jmkao/rfglow/arduino/rfglow_esp32/src/leds.cpp

#include "leds.h"

// TLC59116 Setup
TLC59116Manager tlcmanager(Wire, 30000L);
TLC59116* driver = NULL;

// LED state
int mH = 0;
int mS = 255;
int mB = 0;

unsigned int ma = 61;

// Targets for fading
target_color target = {mH, mS, mB, 0};

int target_maLevel = 1;
long fade_dH = 0, fade_dS = 0, fade_dV = 0;
unsigned long fade_start_ms = 0;

boolean isAutoCycle = false;

unsigned long prevMs = 0;

void initLEDs() {
  // Init TLC59116
  tlcmanager.init();
  DEBUG_PRINTLN("tlcmanager init complete");
  
  driver = &(tlcmanager[0]);
  driver->enable_outputs(true);
  DEBUG_PRINTLN("tlcmanager enable_outputs");
  driver->set_milliamps(ma);
}

void ledTick() {
  unsigned long curMs = millis();

  if (curMs - prevMs < LED_TICK_INTERVAL) {
    return;
  }

  if (isAutoCycle) {
    if (curMs - prevMs > AUTO_INTERVAL) {
      target.h = (target.h + 60) % 360;
    }
  }

  if (fade_start_ms == 0 || target.ms == 0  // No fade in progress
      || curMs - fade_start_ms > 60000  //Fade timed out, more than 60s elapsed
      || curMs - fade_start_ms > target.ms  //Fade reached the end
      ) {
    mH = target.h;
    mS = target.s;
    mB = target.v;
    fade_start_ms = 0;
    target.ms = 0;
  } else if (target.ms == 65535) {
    // Code for UO decay
  } else {
    // In the middle of a linear fade
    long dT = curMs - fade_start_ms;
    long ratio = 10000 - (dT * 10000 / target.ms);
    //DEBUG_PRINTLN("Fade at "+ratio/100+"%");
    int dH = ratio * fade_dH / 10000;
    int dS = ratio * fade_dS / 10000;
    int dV = ratio * fade_dV / 10000;

    mH = (int)target.h - dH;
    if (mH >= 360) {
      mH -= 360;
    } else if (mH < 0) {
      mH += 360;
    }
    mS = target.s - dS;
    mB = target.v - dV;
  }

  setHSVRaw(mH, mS, mB, target_maLevel);
  prevMs = curMs;
}

void toggleAutocycle() {
  isAutoCycle = !isAutoCycle;
}

void stopAutocycle() {
  isAutoCycle = false;
}

void setupFlashLED() {
  driver->set_milliamps(10);
  driver->pattern(0b1000000000000000);
  delay(50);
  driver->pattern(0b0000010000000000);
  delay(50);
  driver->pattern(0b0000000000010000);
  delay(50);
  driver->pattern(0b0000000000000000);
  driver->set_milliamps(ma);

  // driver->enable_outputs(false);  
}

void changeTarget(target_color target) {
  if (target.ms == 0) {
    switchLedTo(target.h, target.s, target.v);
  } else {
    fadeLedTo(target.h, target.s, target.v, target.ms);
  }
}

void switchLedTo(unsigned int h, unsigned int s, unsigned int v) {
  DEBUG_PRINTLN("switchLedTo() called: "+h+" "+s+" "+v);
  target.h = h;
  target.s = s;
  target.v = v;

  target_maLevel = target.h / 360;
  target.h = target.h % 360;

  target.ms = 0;
  fade_start_ms = 0;
}

void fadeLedTo(unsigned int h, unsigned int s, unsigned int v, unsigned int fade_ms) {
  DEBUG_PRINTLN("fadeLedTo() called: "+h+" "+s+" "+v+" "+fade_ms);
  target.h = h;
  target.s = s;
  target.v = v;

  target_maLevel = target.h / 360;
  target.h = target.h % 360;

  target.ms = fade_ms;
  fade_start_ms = millis();

  fade_dH = (int)target.h - (int)mH;
  if (fade_dH > 180) {
    fade_dH -= 360;
  } else if (fade_dH <= -180) {
    fade_dH += 360;
  }
      
  fade_dS = (int)target.s - (int)mS;
  fade_dV = (int)target.v - (int)mB;
  //DEBUG_PRINTLN("Fade deltas dH, dS, dV = "+fade_dH+", "+fade_dS+", "+fade_dV);

}

target_color getCurrentTarget() {
  unsigned long curMs = millis();
  if (fade_start_ms == 0 || target.ms == 0  // No fade in progress
      || curMs - fade_start_ms > 60000  //Fade timed out, more than 60s elapsed
      || curMs - fade_start_ms > target.ms  //Fade reached the end
      ) {
    target_color currentTarget = {target.h, target.s, target.v, 0};
    return currentTarget;
  } else {
    // We're in the middle of the fade
    unsigned long elapsed_fade_ms = curMs - fade_start_ms;
    unsigned long remaining_fade_ms = target.ms - elapsed_fade_ms;

    target_color currentTarget = {target.h, target.s, target.v, remaining_fade_ms};
    return currentTarget;
  }
}

target_color getCurrentCmdColor() {
  target_color currentCmdColor = getCurrentTarget();
  currentCmdColor.h += target_maLevel*360;

  return currentCmdColor;
}

/*
void setHSV(unsigned int h, unsigned int s, unsigned int v) {
  DEBUG_PRINTLN("setHSV() called: "+h+" "+s+" "+v);
  unsigned char maLevel = h / 360;
  h = h % 360;

  //DEBUG_PRINTLN("maLevel = "+maLevel+", h = "+h);

  setHSVRaw(h,s,v,maLevel);
}
*/

void setHSVRaw(unsigned int h, unsigned int s, unsigned int v, int maLevel) {
  
  //DEBUG_PRINTLN("setHSVRaw() called: "+h+" "+s+" "+v+" "+maLevel);
  
  unsigned char r, g, b;
  unsigned char region, remainder, p, q, t, newMa;

  switch (maLevel) {
    case 1:
      newMa = 61;
      break;
    case 2:
      newMa = 21;
      break;
    case 3:
      newMa = 10;
      break;
    case 0:
      newMa = 120;
      break;
    default:
      newMa = ma;
  }

  if (v == 0) {
    newMa = 0;
  }

  if (newMa != ma) {
    driver->set_milliamps(newMa);
    //DEBUG_PRINTLN("set_milliamps to "+newMa);
    ma = newMa;
  }


  if (ma == 120) {
    // Max possible brightness across multiple LEDs if at max power
    if (s == 0) {
      r = v;
      g = v;
      b = v;
    } else {
      region = h / 60;
      remainder = (h - (region * 60)) * 6; 
  
      p = (v * (255 - s)) >> 8;
      q = (v * (255 - ((s * remainder) >> 8))) >> 8;
      t = (v * (255 - ((s * (255 - remainder)) >> 8))) >> 8;
  
      switch (region) {
        case 0:
            r = v; g = t; b = p;
            break;
        case 1:
            r = q; g = v; b = p;
            break;
        case 2:
            r = p; g = v; b = t;
            break;
        case 3:
            r = p; g = q; b = v;
            break;
        case 4:
            r = t; g = p; b = v;
            break;
        default:
            r = v; g = p; b = q;
            break;
      }
    }
  } else {
    // otherwise maintain constant brightness
    unsigned int tempH = h*96/45;
    uint8_t tempS = s;
    uint8_t tempV = v;
  
    uint8_t temp[5];
    uint8_t n = (tempH >> 8);
    //DEBUG_PRINTLN("Converted hue = "+tempH+" Color wheel section = "+n);
    temp[0] = temp[3] = (uint8_t)((                                        (tempS ^ 255)  * tempV) / 255);
    temp[1] = temp[4] = (uint8_t)((((( (tempH & 255)        * tempS) / 255) + (tempS ^ 255)) * tempV) / 255);
    temp[2] =          (uint8_t)(((((((tempH & 255) ^ 255) * tempS) / 255) + (tempS ^ 255)) * tempV) / 255);
    r  = temp[n + 2];
    g = temp[n + 1];
    b  = temp[n    ];
  }
  
  setRGBRaw(r, g, b);
}

void disableOutputs() {
  driver->pattern(0x0000);
  // driver->set_milliamps(120); // Doesn't have any effect on leakage
  driver->enable_outputs(false);
}

void enableOutputs() {
  driver->set_milliamps(ma);
  driver->enable_outputs(true);
}

void setRGBRaw(unsigned char r, unsigned char g, unsigned char b) {
  
  if (r==0 && g==0 && b==0) {
    if (driver->is_enabled()) {
      disableOutputs();
    }
  } else {
    //DEBUG_PRINTLN("setRGBRaw() called: "+r+" "+g+" "+b);
    if (!driver->is_enabled()) {
      enableOutputs();
    }
    
    byte leds[16];
    
    for (int i=0;i<5;i++) {
      // Set red channels
      leds[i] = r;
    }
    
    for (int i=5;i<10;i++) {
      // Set green channels
      leds[i] = g;
    }
    
    for (int i=11;i<16;i++) {
      // Set blue channels;
      leds[i] = b;
    }
    
    driver->set_outputs(leds);
  }
}

void vbatLEDOn() {
   // Check battery voltage and show as color during init delays
  float vBat = vbatRead();
  DEBUG_PRINTLN("vBAT = "+vBat);
  if (vBat > 3.93) {
    setRGBRaw(0,0,20);
  } else if (vBat > 3.7) {
    setRGBRaw(0,20,5);
  } else if (vBat > 3.42) {
    setRGBRaw(16, 15, 0);
  } else {
    setRGBRaw(20, 0, 0);
  }
}
